LDO75/XIN_Power/firmware/current/02_Application/Core/SRC/splash_logo_data.c

/* Generated from Assets/XIN_Power_logo_original.png; do not hand-edit. */
#include "splash_logo.h"
const uint8_t g_splash_logo_rle[] = {
  0xFF, 0x83, 0x08, 0x41, 0x83, 0x08, 0xFF, 0x83, 0x08, 0x41, 0x83, 0x08, 0xFF, 0x83, 0x08, 0x41, 0x83, 0x08,
  0xFF, 0x83, 0x08, 0x41, 0x83, 0x08, 0xFF, 0x83, 0x08, 0x41, 0x83, 0x08, 0xFF, 0x83, 0x08, 0x41, 0x83, 0x08,
  0xFF, 0x83, 0x08, 0x41, 0x83, 0x08, 0xFF, 0x83, 0x08, 0x41, 0x83, 0x08, 0xFF, 0x83, 0x08, 0x41, 0x83, 0x08,
  0xFF, 0x83, 0x08, 0x41, 0x83, 0x08, 0xFF, 0x83, 0x08, 0x41, 0x83, 0x08, 0xFF, 0x83, 0x08, 0x41, 0x83, 0x08,
  0xFF, 0x83, 0x08, 0x41, 0x83, 0x08, 0xFF, 0x83, 0x08, 0x41, 0x83, 0x08, 0xFF, 0x83, 0x08, 0x41, 0x83, 0x08,
  0xFF, 0x83, 0x08, 0x41, 0x83, 0x08, 0xFF, 0x83, 0x08, 0x41, 0x83, 0x08, 0xFF, 0x83, 0x08, 0x41, 0x83, 0x08,
  0xFF, 0x83, 0x08, 0x41, 0x83, 0x08, 0xFF, 0x83, 0x08, 0x41, 0x83, 0x08, 0xFF, 0x83, 0x08, 0x41, 0x83, 0x08,
  0xFF, 0x83, 0x08, 0x41, 0x83, 0x08, 0xFF, 0x83, 0x08, 0x41, 0x83, 0x08, 0xFF, 0x83, 0x08, 0x41, 0x83, 0x08,
  0xFF, 0x83, 0x08, 0x41, 0x83, 0x08, 0xFF, 0x83, 0x08, 0x41, 0x83, 0x08, 0xFF, 0x83, 0x08, 0x41, 0x83, 0x08,
  0xFF, 0x83, 0x08, 0x41, 0x83, 0x08, 0xFF, 0x83, 0x08, 0x41, 0x83, 0x08, 0xFF, 0x83, 0x08, 0x41, 0x83, 0x08,
  0xFF, 0x83, 0x08, 0x41, 0x83, 0x08, 0xFF, 0x83, 0x08, 0x41, 0x83, 0x08, 0xFF, 0x83, 0x08, 0x41, 0x83, 0x08,
  0xFF, 0x83, 0x08, 0x41, 0x83, 0x08, 0xFF, 0x83, 0x08, 0x41, 0x83, 0x08, 0xFF, 0x83, 0x08, 0x41, 0x83, 0x08,
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
  0x01, 0x46, 0x19, 0xE0, 0x83, 0x08, 0x13, 0x83, 0x08, 0x01, 0x14, 0x95, 0x01, 0xB7, 0xAD, 0x01, 0x76, 0x9D,
  0x06, 0x76, 0xA5, 0x01, 0xB7, 0xAD, 0x01, 0xF8, 0xB5, 0x01, 0xF8, 0xAD, 0x03, 0xD8, 0xAD, 0x01, 0xB7, 0xA5,
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
};
const uint32_t g_splash_logo_rle_size = 14241UL;
