LDO75/XIN_Power/firmware/current/05_PC_Tool/xin_power_qt.py

"""XIN Power desktop console: Qt Quick UI with a serial worker."""

from __future__ import annotations

from collections import deque
from pathlib import Path
from queue import Empty, Queue
import csv
import os
import argparse
import json
import sys
from datetime import datetime
import threading
import time

from PySide6.QtCore import QObject, Property, QThread, QTimer, QUrl, Signal, Slot
from PySide6.QtQml import QQmlApplicationEngine
from PySide6.QtQuickControls2 import QQuickStyle
from PySide6.QtWidgets import QApplication, QFileDialog

from device_link import describe_ports
from link_diagnostics import recoverable_serial_failure, describe_serial_failure
from wire_protocol import SerialSession
from readable_log import format_frame, format_command, FAULT_TEXT
from session_record import SessionRecord
from firmware_image import FirmwareImage, load_firmware
from protocol import parse_line, telemetry_number
from updater_protocol import UpgradeError, perform_upgrade
from dac_calibration import CurveCalibration
from pid_tuning import PidTuning


class SerialReader(QThread):
    lineReceived = Signal(str)
    opened = Signal()
    stopped = Signal(str)
    upgradeProgress = Signal(int, str)
    upgradeSucceeded = Signal(str)
    upgradeFailed = Signal(str, bool)

    def __init__(self, port_name: str) -> None:
        super().__init__()
        self.port_name = port_name
        self.commands: Queue[str] = Queue()
        self.frames: Queue = Queue()
        self.urgent = Queue()
        self.stop_event = threading.Event()
        self._upgrade_request: tuple[FirmwareImage, str] | None = None
        self._upgrade_cancel = threading.Event()

    def send(self, command: str) -> None:
        (self.urgent if command in ("OUT OFF","CAL POINT STOP") else self.commands).put(command)

    def stop(self) -> None:
        self.stop_event.set()

    def begin_upgrade(self, image: FirmwareImage, transport: str) -> None:
        # The existing serial handle belongs to this thread. Reuse it rather
        # than closing/reopening a Windows Bluetooth SPP virtual COM port.
        while True:
            try:
                self.commands.get_nowait()
            except Empty:
                break
        self._upgrade_cancel.clear()
        self._upgrade_request = (image, transport)

    def cancel_upgrade(self) -> None:
        self._upgrade_cancel.set()

    def run(self) -> None:
        try:
            import serial
            # Only the explicitly selected port is opened. Short read timeouts
            # let queued commands and disconnect requests run without GUI waits.
            with serial.Serial(self.port_name,115200,timeout=.005,write_timeout=1) as port:
                port.reset_input_buffer();self.opened.emit()
                session=SerialSession(port)
                info=session.handshake(self.stop_event.is_set)
                if info.values.get('hw')!='PY32F403_V2':
                    raise ValueError('选中端口回应的硬件型号不匹配')
                self.frames.put(info)
                # Fresh connection: configure telemetry/read status only. Queued
                # commands from a lost connection are never replayed here.
                try: new_rate = tuple(map(int, info.values.get('fw','0').split('.'))) >= (6,2,2)
                except ValueError: new_rate = False
                if new_rate: session.send('LOG RATE 40')
                self.send('STATUS')
                while not self.stop_event.is_set():
                    request=self._upgrade_request
                    if request is not None and session.pending is None:
                        self._upgrade_request=None
                        image,transport=request
                        def factory(**kwargs):
                            raw=serial.Serial(**kwargs)
                            adapted=SerialSession(raw)
                            try:adapted.handshake(self._upgrade_cancel.is_set)
                            except Exception:raw.close();raise
                            return adapted
                        try:
                            result=perform_upgrade(self.port_name,image,factory,self.upgradeProgress.emit,
                                self._upgrade_cancel.is_set,transport=transport,initial_port=session)
                        except Exception as exc:
                            self.upgradeFailed.emit(str(exc),session.is_open)
                            if not session.is_open:break
                            session.pending=None;self.send('INFO')
                        else:
                            self.upgradeSucceeded.emit(result.new_version);break
                    try:urgent=self.urgent.get_nowait()
                    except Empty:urgent=""
                    if urgent:
                        session.pending=None;session.send(urgent)
                    if session.pending is None:
                        try:command=self.commands.get_nowait()
                        except Empty:command=''
                        if command:
                            try:session.send(command)
                            except (ValueError,OverflowError) as exc:
                                self.frames.put(parse_line('@ERR,cmd=LOCAL,reason='+str(exc)))
                    try:
                        received = session.poll()
                    except TimeoutError:
                        # A missing command ACK is not a broken COM handle.
                        # Keep receiving, report unknown outcome, never replay it.
                        session.pending = None
                        self.frames.put(parse_line('@ERR,cmd=LINK,reason=命令确认超时，结果未知，请读取状态确认'))
                        received = []
                    for frame in received: self.frames.put(frame)
        except Exception as exc:
            self.stopped.emit(describe_serial_failure(str(exc)) if not self.stop_event.is_set() else '')
        else:self.stopped.emit('')


class ProbeScanThread(QThread):
    completed = Signal(object)
    failed = Signal(str)

    def __init__(self, connected_port: str = "", connected_version: str = "") -> None:
        super().__init__()
        self.connected_port = connected_port
        self.connected_version = connected_version

    def run(self) -> None:
        try:
            from serial.tools import list_ports
            # Enumeration never opens ports or probes paired Bluetooth endpoints.
            self.completed.emit([(item.device,f'{item.device}  ·  {item.description}',item.transport,
                                  item.device==self.connected_port)
                                 for item in describe_ports(list_ports.comports())])
        except Exception as exc:self.failed.emit(str(exc))


class Bridge(QObject):
    portsChanged = Signal()
    stateChanged = Signal()
    telemetryChanged = Signal()
    logsChanged = Signal()
    logStateChanged = Signal()
    diagnosticsChanged = Signal()
    updateChanged = Signal()
    calibrationChanged = Signal()

    def __init__(self) -> None:
        super().__init__()
        self.live_api = None
        self._ports: list[str] = []
        self._all_ports = []
        self._transport_mode = "wired"
        self._connecting = False
        self._batching = False
        self._frame_timer = QTimer(self)
        self._frame_timer.setInterval(20)
        self._frame_timer.timeout.connect(self._drain_frames)
        self._frame_timer.start()
        self._record = SessionRecord()
        self._last_telemetry_log = 0.0
        self._vpp = "—"
        self._port_types: dict[str, str] = {}
        self._verified_ports: set[str] = set()
        self._scan_thread: ProbeScanThread | None = None
        self._scanning = False
        self._scan_text = "选择有线或无线，再扫描系统串口"
        self._selected_port = ""
        self._connected = False
        self._connection_text = "未连接"
        self._firmware = "—"
        self._hardware = "—"
        self._voltage = "0.000"
        self._current = "0.000"
        self._input_voltage = "0.000"
        self._power = "0.00"
        self._temperature = "—"
        self._set_voltage = "5.000"
        self._set_current = "0.100"
        self._output_on = False
        self._fault = "NONE"
        self._history_v: deque[float] = deque(maxlen=140)
        self._history_i: deque[float] = deque(maxlen=140)
        self._telemetry_arrivals: deque[float] = deque(maxlen=11)
        self._telemetry_rate_text = "等待遥测"
        self._control_diagnostic = "等待控制状态"
        self._telemetry_rows = deque(maxlen=1000)
        self._session_lines = deque(maxlen=1000)
        self._logs: deque[str] = deque(maxlen=1000)
        self._log_paused = False
        self._paused_log_text = ""
        self._pending_log_count = 0
        self._log_dirty = False
        self._voltage_diagnostic = "读取校准参数后，显示原始电压、增益和偏移；不会自动归零。"
        self._log_timer = QTimer(self)
        self._log_timer.setInterval(100)
        self._log_timer.timeout.connect(self._flush_log_view)
        self._log_timer.start()
        self._worker: SerialReader | None = None
        self._reconnect_pending = False
        self._reconnect_attempts = 0
        self._reconnect_port = ''
        self._image_path = ""
        self._update_progress = 0
        self._update_status = "选择固件文件后可开始升级"
        self._updating = False
        self._calibration_status = "按页面指引采集 5V / 20V 实测值"
        self._calibration_raw: dict[int, int] = {}
        self._calibration_actual: dict[int, float] = {}
        self._capture_pending: tuple[int, float] | None = None
        self._save_pending: tuple[int, int] | None = None
        self.curve = CurveCalibration(
            self.sendCommand,
            lambda: self._connected and not self._updating
                    and self._save_pending is None and self._capture_pending is None,
            self,
        )
        self.pid = PidTuning(self.sendCommand, self)
        self.stateChanged.connect(lambda: self.pid.connection_changed(
            self._connected and not self._updating, self._firmware))
        self._disconnect_after_calibration = False
        self.stateChanged.connect(lambda: self.curve.connection_changed(
            self._connected and not self._updating, self._firmware))

    @Property(QObject, constant=True)
    def pidController(self):
        return self.pid

    @Property("QVariantList", notify=portsChanged)
    def ports(self) -> list[str]:
        return self._ports

    @Property(str, notify=stateChanged)
    def selectedPort(self) -> str:
        return self._selected_port

    @Property(str, notify=stateChanged)
    def selectedTransport(self) -> str:
        return ("蓝牙 SPP" if self._port_types.get(self._selected_port) == "BLUETOOTH SPP"
                else "USB / 串口")

    @Property(str, notify=stateChanged)
    def transportMode(self):return self._transport_mode

    @Property(bool, notify=stateChanged)
    def connecting(self):return self._connecting

    @Property(str, notify=telemetryChanged)
    def vpp(self):return self._vpp

    @Slot(str)
    def selectTransport(self, mode):
        if mode not in ('wired','wireless') or self._worker or self._updating:return
        self._reconnect_pending=False
        self._transport_mode=mode;self._selected_port='';self._filter_ports()

    def _filter_ports(self):
        rows=[row for row in self._all_ports if (row[2]=='BLUETOOTH SPP')==(self._transport_mode=='wireless')]
        self._ports=[row[1] for row in rows]
        self._port_types={row[0]:row[2] for row in self._all_ports}
        if self._selected_port not in {row[0] for row in rows} and not self._worker and not self._reconnect_pending:
            self._selected_port=rows[0][0] if rows else ''
        self._scan_text=(f'找到 {len(rows)} 个'+('已配对蓝牙串口' if self._transport_mode=='wireless' else '有线串口')+
                         '；连接时验证电源身份')
        self.portsChanged.emit();self.stateChanged.emit()

    def _drain_frames(self):
        if not self._worker:return
        self._batching=True;count=0
        try:
            while count<512:
                try:frame=self._worker.frames.get_nowait()
                except Empty:break
                self._on_frame(frame);count+=1
        finally:self._batching=False
        if count:self.telemetryChanged.emit()

    @Property(bool, notify=stateChanged)
    def scanning(self) -> bool:
        return self._scanning

    @Property(str, notify=stateChanged)
    def scanText(self) -> str:
        return self._scan_text
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
